AbhiAlderman/Animatronic-Eyes/eyeanimatronic-main/software/testCode (not useful!)/faceDetection/camera_index.h

//File: index_ov2640.html.gz, Size: 4316
#define index_ov2640_html_gz_len 4316
const uint8_t index_ov2640_html_gz[] = {
0x1f,0x8b,0x08,0x08,0xf2,0x61,0x62,0x5d,0x00,0xff,0x69,0x6e,0x64,0x65,0x78,0x2e,0x68,0x74,0x6d,0x6c,0x2e,0x67,0x7a,0x00,0x5d,0x53,0x5d,0x6f,0xdb,0x3a,0x0c,0x7d,0xf7,0xaf,0xe0,0xd4,0x0d,0x70,0xd0,0xc6,0x4e,0xee,0xc3,0x10,0xa4,0x76,0x1e,0x7a,0xd7,0x61,0x03,0x3a,0x14,0x58,0x37,0xf4,0x71,0x55,0x24,0xc6,0xd1,0x6a,0x4b,0x81,0xa4,0xc4,0x0d,0x0a,0xff,0xf7,0x52,0xfe,0x4a,0xba,0x24,0x08,0x65,0xf2,0xf0,0xf0,0x90,0xa2,0xb3,0x0f,0xd2,0x08,0x7f,0xdc,0x21,0x6c,0x7d,0x55,0xae,0xa2,0x6c,0x30,0xc8,0x25,0x99,0x0a,0x3d,0x07,0xb1,0xe5,0xd6,0xa1,0xcf,0xd9,0xde,0x6f,0xa6,0x0b,0x36,0xb8,0x35,0xaf,0x30,0x67,0x07,0x85,0xf5,0xce,0x58,0xcf,0x40,0x18,0xed,0x51,0x13,0xac,0x56,0xd2,0x6f,0x73,0x89,0x07,0x25,0x70,0xda,0x3e,0x5c,0x29,0xad,0xbc,0xe2,0xe5,0xd4,0x09,0x5e,0x62,0x3e,0x0f,0x1c,0x5e,0xf9,0x12,0x57,0x5f,0xb9,0x40,0xf8,0x65,0xb9,0x78,0x56,0xba,0xc8,0xd2,0xce,0x19,0x65,0xce,0x1f,0x83,0x5d,0x1b,0x79,0x84,0xd7,0x08,0xc2,0x67,0x4d,0x98,0xc2,0x9a,0xbd,0x96,0x4b,0xb8,0x98,0x2f,0xc2,0xf7,0x3a,0x6a,0xa2,0x0b,0xe7,0x2d,0xf2,0x6a,0x1a,0xaa,0x73,0xa5,0xd1,0x0e,0xf8,0x8a,0xbf,0x74,0xc5,0x97,0xf0,0x79,0x36,0xdb,0xbd,0x9c,0x81,0x07,0x48,0x1f,0x9e,0xcf,0x66,0x9f,0x42,0x34,0x4b,0xfb,0xb2,0x59,0xda,0xb7,0x1f,0xea,0x93,0x91,0xea,0x00,0x4a,0xe6,0xac,0xef,0x70,0x5a,0xe2,0xc6,0x53,0x0b,0x00,0x63,0xe4,0x5f,0x11,0x34,0x8d,0x92,0x3b,0x97,0x33,0x55,0xf1,0x02,0xcf,0xfc,0x2b,0xc8,0x54,0x55,0x9c,0xe5,0x30,0x70,0x56,0xe4,0x2c,0x04,0x52,0x62,0x0b,0xc5,0x3b,0xe3,0x84,0x55,0x3b,0xbf,0x8a,0xe8,0x7e,0xf6,0x15,0x55,0x4d,0xb8,0x94,0xb7,0x07,0x3a,0xdc,0x29,0x47,0x2a,0xd0,0xc6,0xec,0xcb,0xfd,0x8f,0xff,0x3b,0x49,0x77,0x86,0x4b,0x94,0xec,0x0a,0x36,0x7b,0x2d,0xbc,0x32,0x3a,0xc6,0x00,0x9d,0x50,0xa7,0x24,0xf3,0xc0,0x2d,0x8d,0xcf,0xe1,0x37,0xe3,0x3c,0xe4,0x30,0x32,0x96,0x46,0xf0,0x00,0x4e,0x8c,0x55,0x85,0xd2,0xd7,0x04,0x25,0xa5,0x84,0x79,0x7c,0xf8,0xf3,0xfb,0xe7,0x1d,0x41,0x59,0xed,0x96,0x69,0xca,0xe0,0x92,0x66,0xa5,0xa5,0xa9,0x4f,0x29,0xdb,0xc0,0x75,0x09,0x6c,0xb9,0xf8,0x8f,0x9d,0x12,0x6b,0x47,0x49,0x1a,0x6b,0x78,0xc4,0xf5,0x83,0x11,0xcf,0xe8,0xe3,0x8e,0x6b,0x72,0xc2,0x84,0x8d,0x39,0x57,0x51,0xa0,0xbf,0x2d,0x31,0x1c,0x6f,0x8e,0xdf,0x65,0x3c,0xcc,0xa5,0xcd,0xa0,0x5f,0xed,0x12,0xa3,0xcd,0x0e,0x35,0xe5,0xc4,0x13,0xc8,0x57,0xfd,0xed,0x05,0x32,0x53,0x22,0x29,0x2a,0xe2,0x27,0x1a,0x83,0x46,0xe1,0x51,0x82,0x37,0xf0,0xf1,0xb5,0xab,0xd9,0x3c,0xb5,0x1c,0x4d,0xf8,0x6b,0x59,0x2a,0x74,0x8e,0xae,0x83,0x88,0xc6,0xd3,0xc0,0xa6,0x36,0x10,0x87,0xd7,0xc0,0x6c,0x86,0x58,0x22,0x39,0x2d,0x79,0x9e,0xd3,0x10,0x48,0x11,0x6d,0x27,0x0b,0xd3,0x6c,0xf7,0x26,0x4d,0x41,0x9b,0x01,0xe7,0x80,0xfb,0xaa,0xf5,0x37,0x23,0xd3,0x3b,0x0a,0x45,0x4d,0x73,0x2d,0x02,0xf5,0x4d,0x69,0xd6,0x23,0x4b,0x7b,0x2d,0x7b,0x5b,0xde,0xaf,0xff,0x92,0x74,0x12,0x45,0x92,0x13,0x41,0xbd,0x7b,0xec,0x5c,0xf4,0xfc,0x8e,0xa9,0xed,0xa6,0x4d,0xa4,0x09,0x26,0xb4,0x36,0x94,0x33,0xe6,0x77,0xb1,0x20,0xa1,0x89,0x1a,0x42,0xd2,0x32,0xf7,0x0b,0x94,0xa5,0xfd,0x1a,0xa7,0xed,0xbb,0xfd,0x06,0x2b,0x33,0xa7,0x29,0xf2,0x03,0x00,0x00
};
